j5ik2o/dgx-spark-rack/models/spark-rack/reference/joint-illustrations-20261009/README.md

# 全体構想図へ添える接合部の参照図

2026年10月9日の検査済み実行から、接合状態と挿入順の図3枚、検査結果を内容を変えずに保全しました。元の生成記録も添えています。元の記録は全生成物を対象としますが、このフォルダは図の参照に必要な部分だけです。

形状の正本は`models/spark-rack/source/freecad_spark_rack_joint_coupons.py`です。この図から造形データを作りません。試験片の印刷と実物確認は後回しです。
