j5ik2o/dgx-spark-rack/print-projects/spark-rack/prototype/modular-spark-rack-pla-fit-tests.3mf

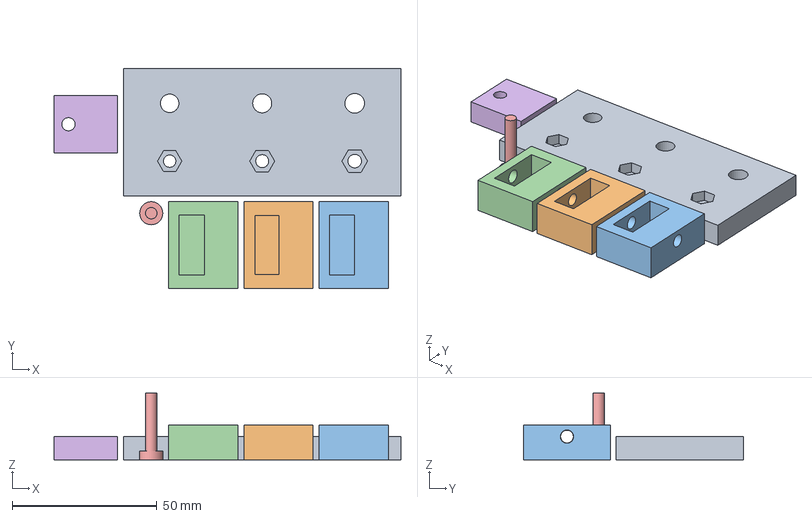
[picture p24: CAD file, 2026-09-22]
print-projects/spark-rack/prototype/modular-spark-rack-pla-fit-tests.3mf
120.0 x 76.0 x 23.0 mm
hardware_coupon.stl
fit_coupon_020.stl
fit_coupon_030.stl
fit_coupon_040.stl
locking_pin.stl
bar_coupon.stl
