j5ik2o/dgx-spark-rack/print-projects/spark-rack/prototype/modular-spark-rack-pla-frame-without-pins.3mf

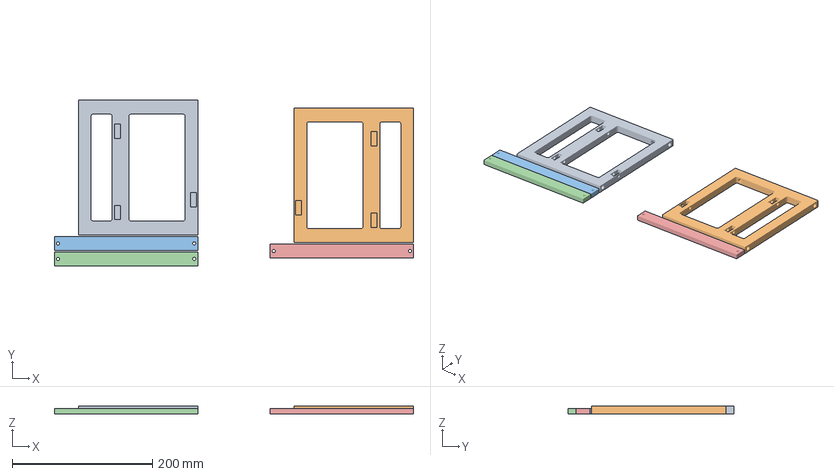
[picture p25: CAD file, 2026-09-22]
print-projects/spark-rack/prototype/modular-spark-rack-pla-frame-without-pins.3mf
511.2 x 236.0 x 12.0 mm
side_L.stl
side_R.stl
crossbar.stl x 3
