j5ik2o/dgx-spark-rack/exports/freecad/parts/stack_locator.step

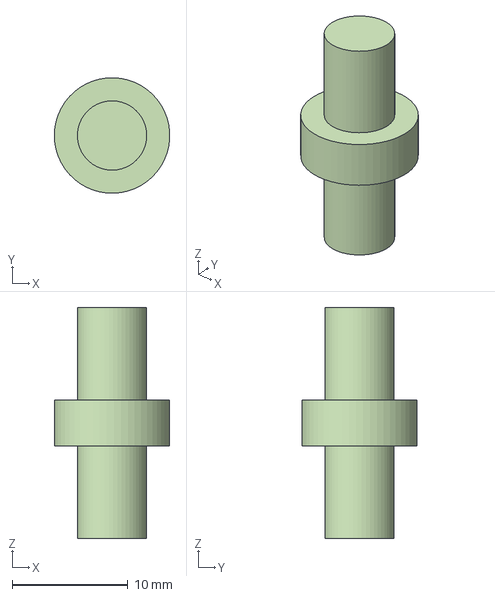
[picture p26: CAD file, 2026-09-16]
exports/freecad/parts/stack_locator.step
9.99 x 10.00 x 20.0 mm
