j5ik2o/dgx-spark-rack/exports/freecad/parts/fit_coupon_040.step

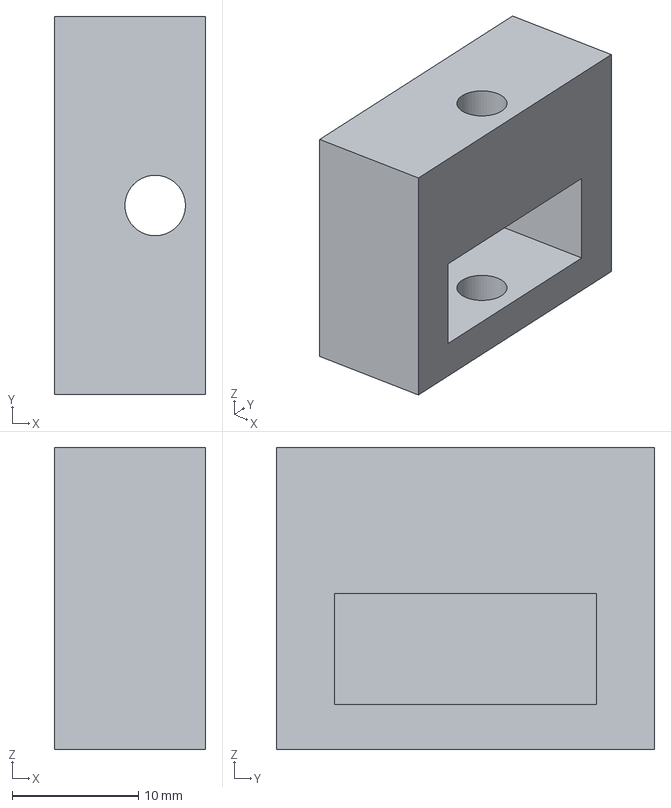
[picture p27: CAD file, 2026-09-16]
exports/freecad/parts/fit_coupon_040.step
12.0 x 30.0 x 24.0 mm
