j5ik2o/dgx-spark-rack/exports/freecad/parts/crossbar.step

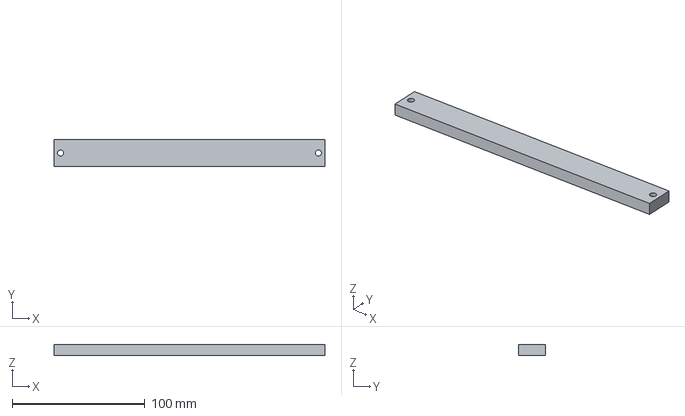
[picture p28: CAD file, 2026-09-16]
exports/freecad/parts/crossbar.step
204.0 x 20.0 x 8.00 mm
