j5ik2o/dgx-spark-rack/exports/freecad/parts/locking_pin.step

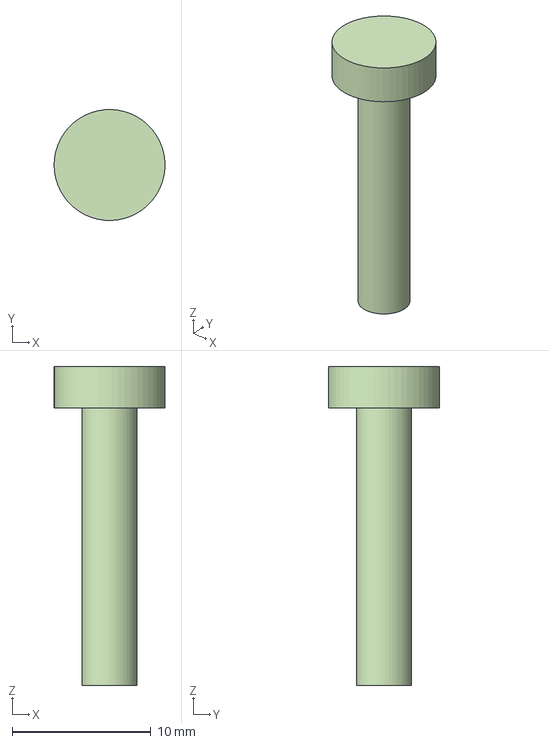
[picture p29: CAD file, 2026-09-16]
exports/freecad/parts/locking_pin.step
7.99 x 8.00 x 23.0 mm
