j5ik2o/dgx-spark-rack/print-projects/adapter-rack/prototype/README.md

# 試作用印刷設定

PLAで仮組みするための3MFです。本番用ではありません。`mise run 3mf:prototype:adapter-rack` で `generated/<実行ID>/` に生成します。採用した手調整済み3MFはこのフォルダへ別名保存します。[操作手順](../../../docs/タスクランナー.md)を参照してください。
