j5ik2o/dgx-spark-rack/print-projects/fan-controller/production/README.md

# 本番用印刷設定

本番用3MFはまだありません。素材と印刷条件を決定し、`print-projects/profiles/production/fan-controller.json` を設定してから生成します。[設定方法](../../../docs/タスクランナー.md)を参照してください。
